foorschtbar/mains-frequency-measure/Circuit & Board/B_Cu.PNG

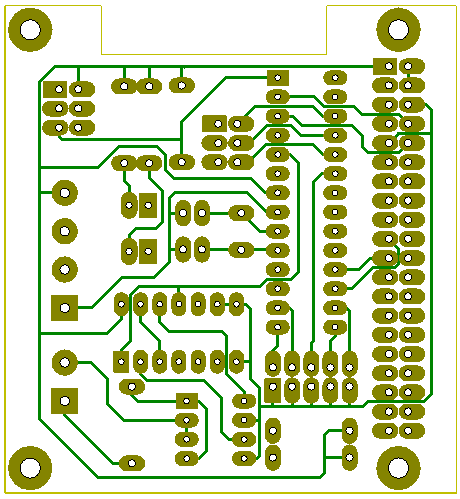
Circuit & Board/B_Cu.PNG
