foorschtbar/mains-frequency-measure/Circuit & Board/Bauteile.PNG

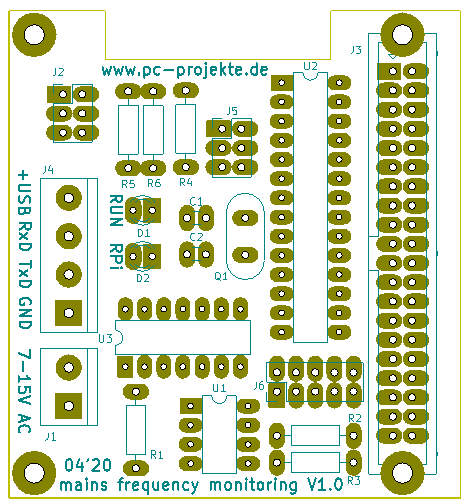
Circuit & Board/Bauteile.PNG
