foorschtbar/mains-frequency-measure/Circuit & Board/mfm_1.jpg

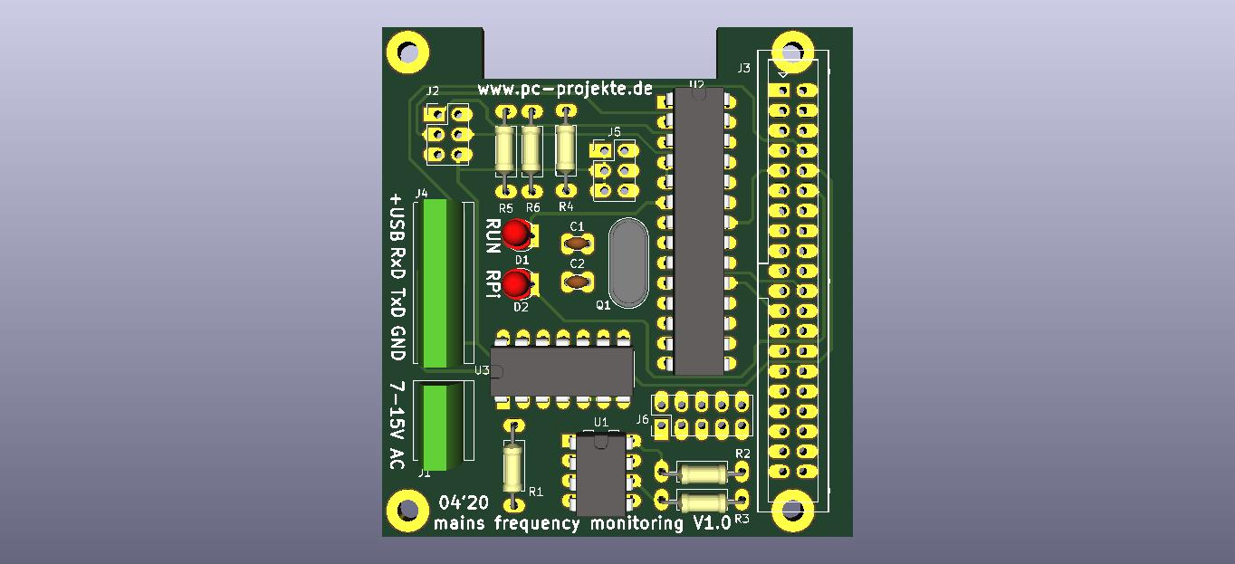
Circuit & Board/mfm_1.jpg
