foorschtbar/mains-frequency-measure/Circuit & Board/mfm_1x.jpg

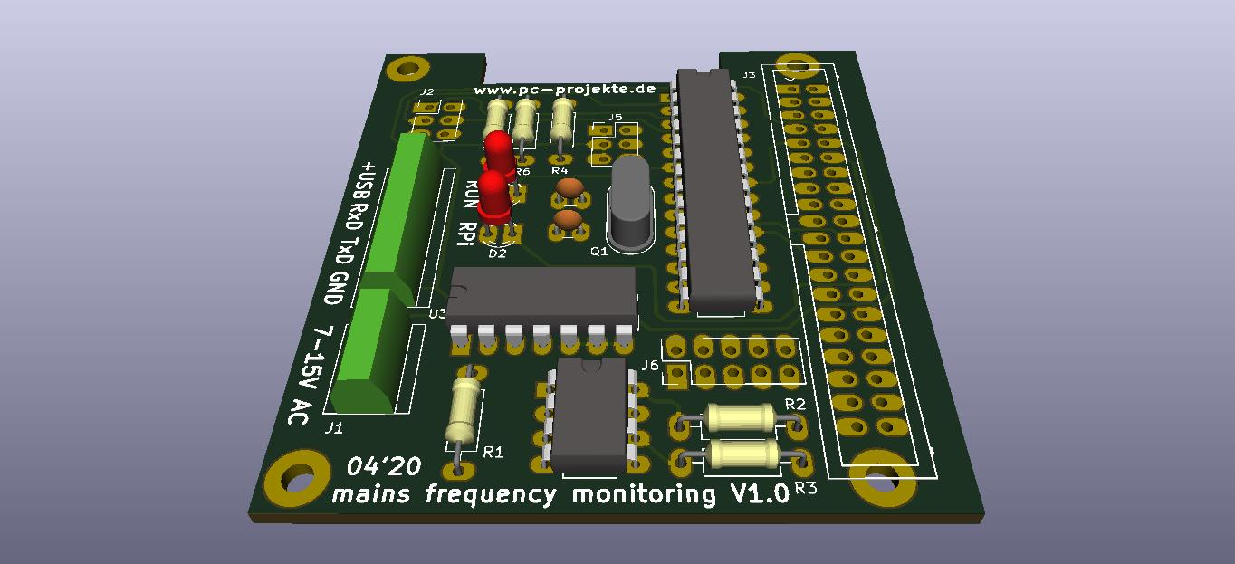
Circuit & Board/mfm_1x.jpg
