foorschtbar/mains-frequency-measure/Circuit & Board/Schaltplan.png

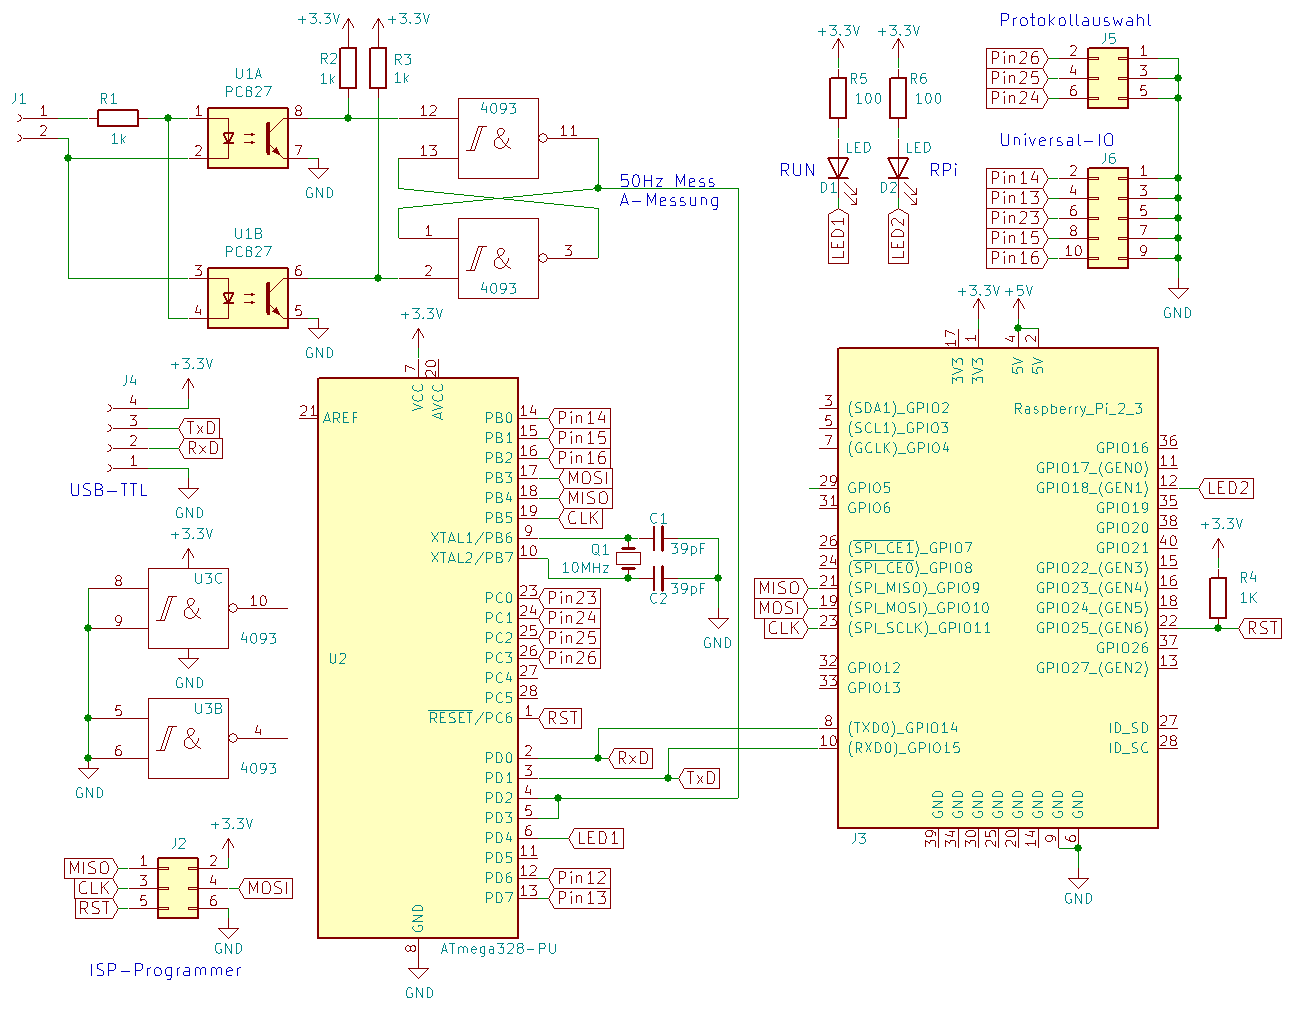
Circuit & Board/Schaltplan.png
