foorschtbar/mains-frequency-measure/Graphics/Netzpendelung.png

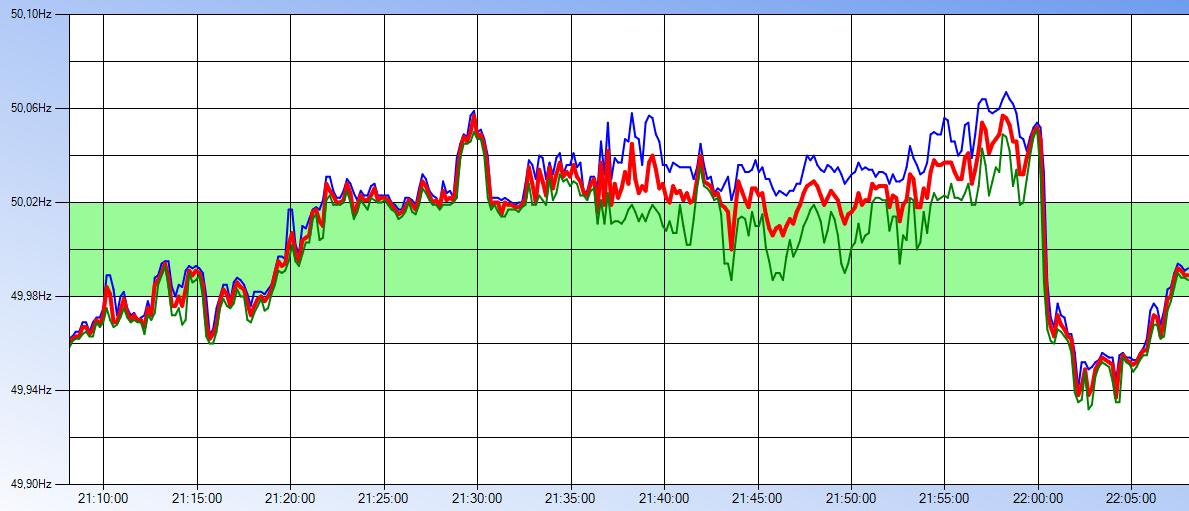
Graphics/Netzpendelung.png
