foorschtbar/mains-frequency-measure/Picture/Pic011.jpg

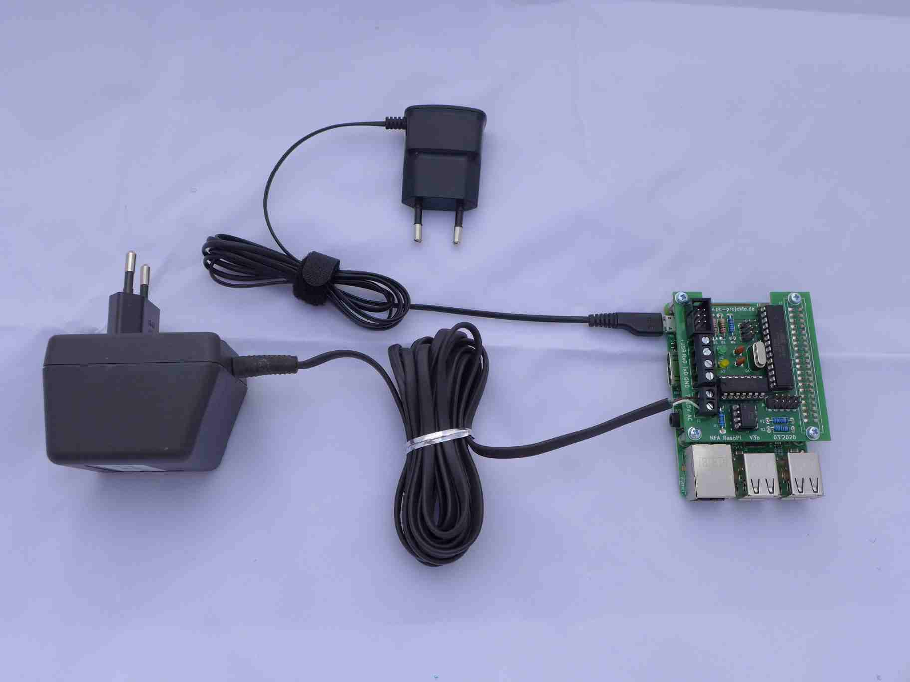
Picture/Pic011.jpg
